Andreas-Wahl/Startlight-HW/#PDF/PCB2/PCB2_Display-B_Cu.pdf

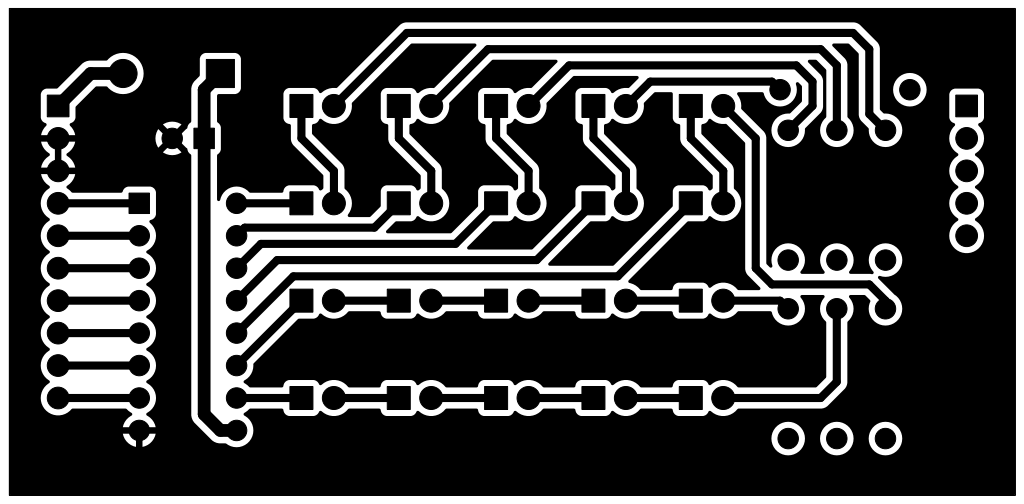
[picture p44: page 1]

https://www.andreas-wahl.de/
File: PCB2_Display.kicad_pcb Sheet: Andreas Wahl - Welzheim
