Andreas-Wahl/Startlight-HW/#PDF/PCB2/PCB2_Display-F_Cu.pdf

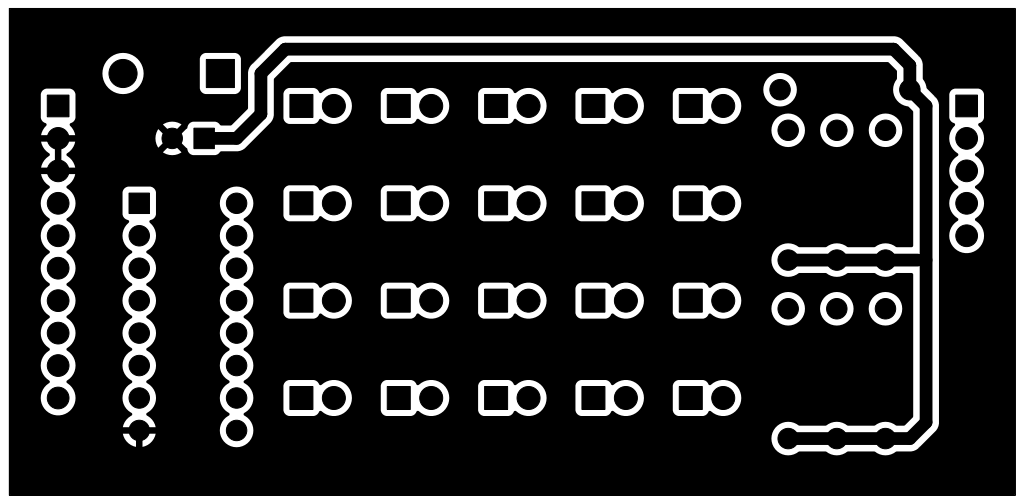
[picture p47: page 1]

https://www.andreas-wahl.de/
File: PCB2_Display.kicad_pcb Sheet: Andreas Wahl - Welzheim
