Andreas-Wahl/Startlight-HW/#PDF/PCB2/PCB2_Display-F_Mask.pdf

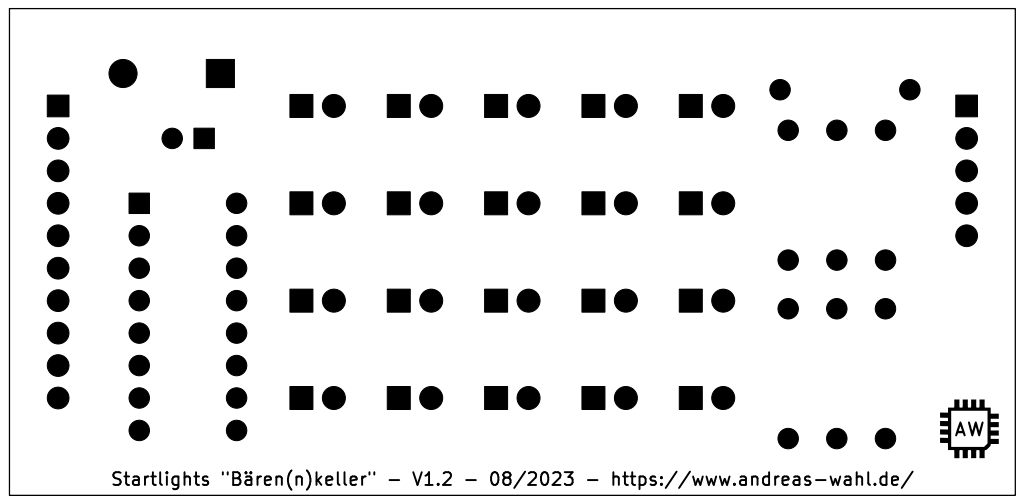
[picture p48: page 1]

https://www.andreas-wahl.de/
File: PCB2_Display.kicad_pcb Sheet: Andreas Wahl - Welzheim
