Andreas-Wahl/Startlight-HW/LtSpice/Filter_cutoff-frequency.asc

C1: cap; 2n2
R1: res; 1k8
R2: res; 1k0
V1: voltage; ""; AC 1
Named nets: OUT, IN, 0
.ac dec 100 100 1meg
.meas AC peak max mag(V(out))
.meas AC fcutoff when mag(V(out))=peak/sqrt(2) fall=1
Startampel "Bären(n)keller" - AC-Analyse Eingangsfilter
